viuhimciuc/Cartridge-SEGA/GEN-CART-171-6329A-7147A/Documents/GEN-CART-171-6329A-7147A.png

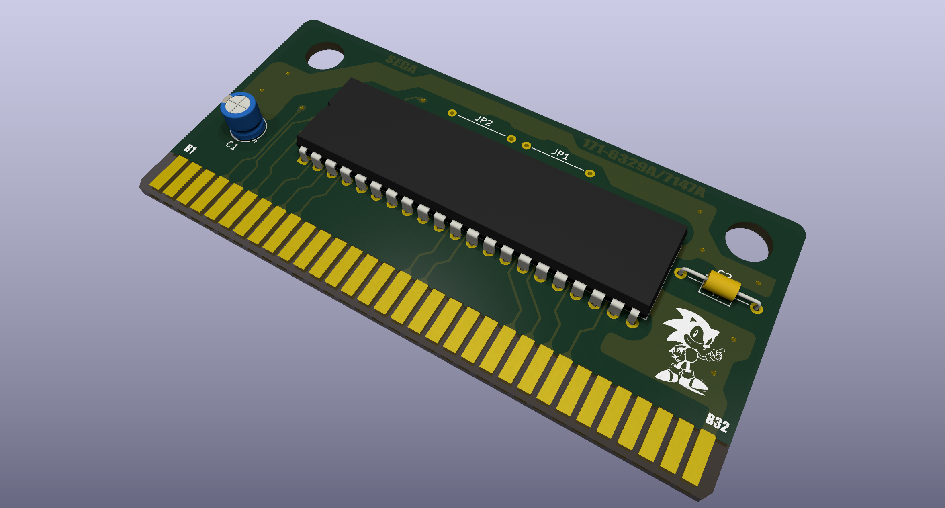
GEN-CART-171-6329A-7147A/Documents/GEN-CART-171-6329A-7147A.png
