viuhimciuc/Cartridge-SEGA/GEN-CART-171-6570A/Documents/GEN-CART-171-6570A.png

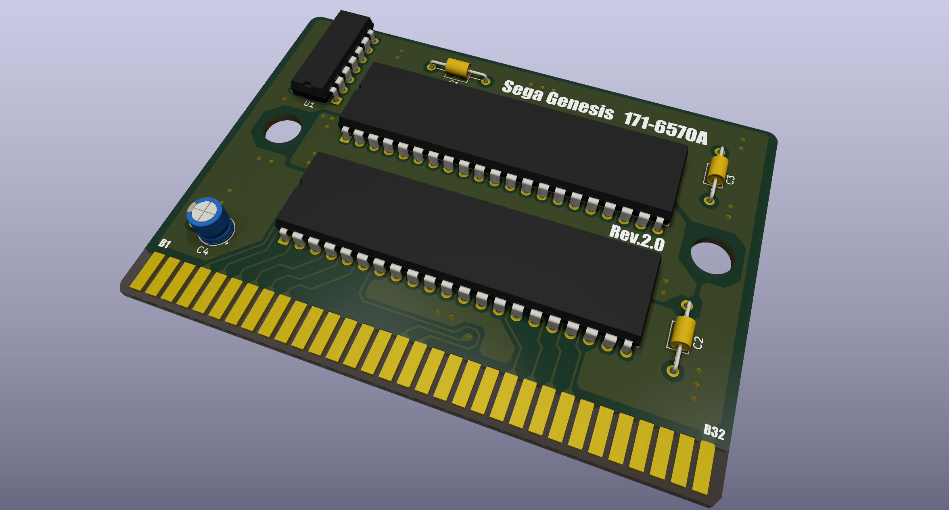
GEN-CART-171-6570A/Documents/GEN-CART-171-6570A.png
