viuhimciuc/Cartridge-SEGA/GEN-CART-171-6570A_MultiGames/Documents/GEN-CART-171-6570A_MultiGames_bottom.png

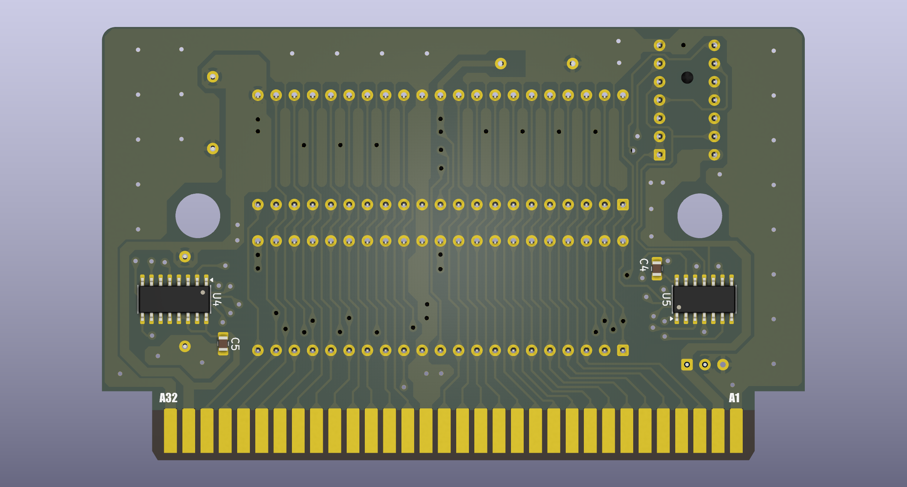
GEN-CART-171-6570A_MultiGames/Documents/GEN-CART-171-6570A_MultiGames_bottom.png
