viuhimciuc/Cartridge-SEGA/TSOP_Adapter_M29FxxxF/TSOP_Adapter_M29FxxxF.png

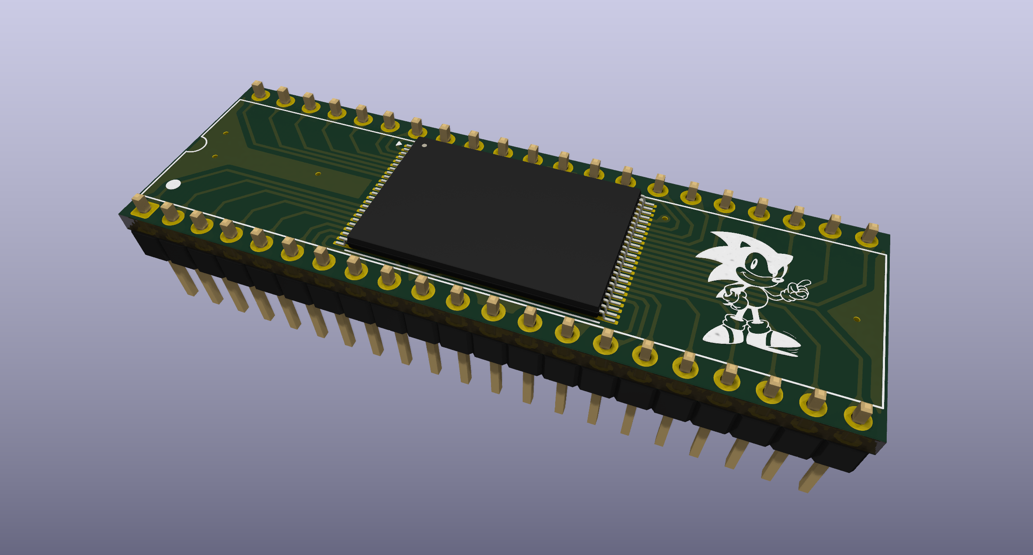
TSOP_Adapter_M29FxxxF/TSOP_Adapter_M29FxxxF.png
